reineydays/reine-performing-robots/First_Robot_Spin.ino

/*
  Terribly simple robot
  Based on Adafruit DCMotorTest
  11 Sept 2017 - Michael Shiloh - Program creation
*/

#include <Wire.h>
#include <Adafruit_MotorShield.h>
#include "utility/Adafruit_MS_PWMServoDriver.h"

// Create the motor shield object with the default I2C address
Adafruit_MotorShield AFMS = Adafruit_MotorShield();

Adafruit_DCMotor * rightMotor = AFMS.getMotor(1);
Adafruit_DCMotor * leftMotor = AFMS.getMotor(4);

void setup() {
  Serial.begin(9600);    

  AFMS.begin();  

}

void loop() {

  goForward();
  delay (100); 
  stop();       
  delay (250);  

  turnRight(300); 

  goForward();
  delay (100);
  stop();
  delay (250);

  turnRight(300);
 
  goForward();
  delay (100);
  stop();
  delay (250);

  turnRight(300);
 
 
}

void goForward() {
  Serial.println("goForward");
  leftMotor->setSpeed(150);
  leftMotor->run(FORWARD);
  rightMotor->setSpeed(150);
  rightMotor->run(FORWARD);
}

void stop() {
  Serial.println("stop");
  leftMotor->run(RELEASE);
  rightMotor->run(RELEASE);
}

void turnRight(int amount) {
  Serial.println("turnRight");
  leftMotor->setSpeed(250);
  leftMotor->run(FORWARD);
  rightMotor->setSpeed(50);
  rightMotor->run(BACKWARD);
  delay (amount);
  stop();
  delay (250);
}

void turnLeft() {
  Serial.println("turnLeft");
  leftMotor->setSpeed(250);
  leftMotor->run(BACKWARD);
  rightMotor->setSpeed(50);
  rightMotor->run(FORWARD);
}

void testRobot() {
  // do a little test:
  // Go forward for a bit
  leftMotor->setSpeed(150);
  leftMotor->run(FORWARD);
  rightMotor->setSpeed(150);
  rightMotor->run(FORWARD);
  delay (500);

  // stop for a moment before changing direction
  // to avoid stressing the motor
  leftMotor->run(RELEASE);
  rightMotor->run(RELEASE);
  delay (250);

  // Go backwards for a bit
  leftMotor->setSpeed(150);
  leftMotor->run(BACKWARD);
  rightMotor->setSpeed(150);
  rightMotor->run(BACKWARD);
  delay (500);

  // and stop.
  // Note that the  comment in the example is wrong:
  // RELEASE turns the motor OFF
  leftMotor->run(RELEASE);
  rightMotor->run(RELEASE);
}
